Egray180/night-vision-monocular/resources/switch-16.snapshot.3/switch_SS12F15G5_4.png

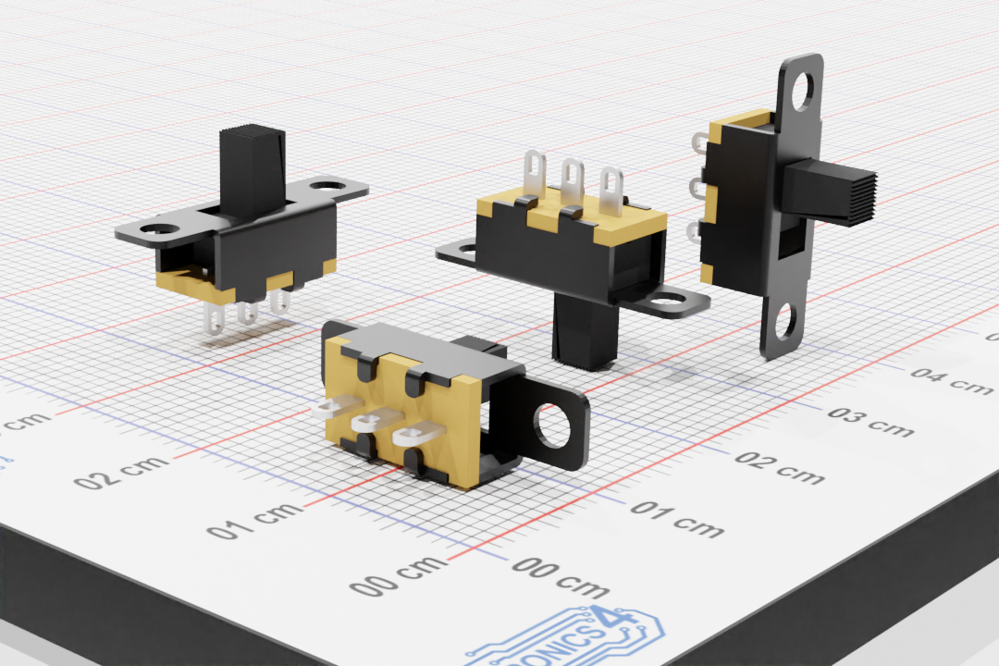
resources/switch-16.snapshot.3/switch_SS12F15G5_4.png
