Egray180/night-vision-monocular/resources/raspberry-pi-zero-2-w-1.snapshot.3/Crystal Resonator, Raspberry Pi Zero 2 W.SLDPRT

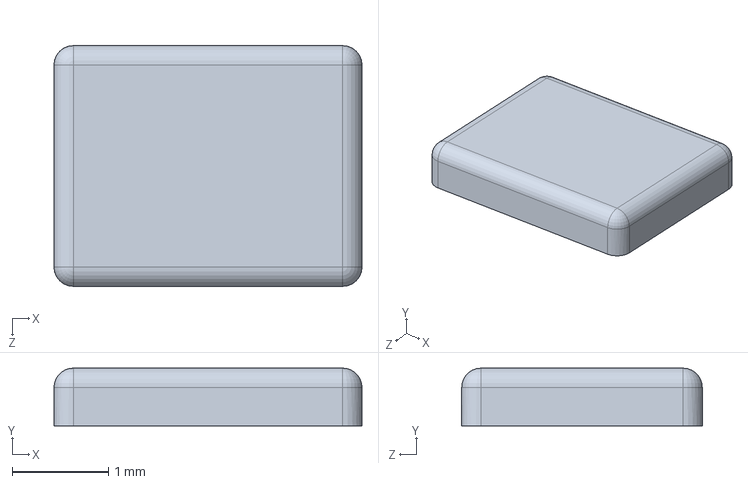
[picture p42: CAD file, 2024-07-07]
resources/raspberry-pi-zero-2-w-1.snapshot.3/Crystal Resonator, Raspberry Pi Zero 2 W.SLDPRT
3.20 x 0.6 x 2.50 mm
