Egray180/night-vision-monocular/resources/raspberry-pi-zero-2-w-1.snapshot.3/PAM2306AYPKE, Switching Voltage Regulators Dual PWM Step-Down 40uA 1A 1.5MHz, Raspberry Pi Zero 2 W.SLDPRT

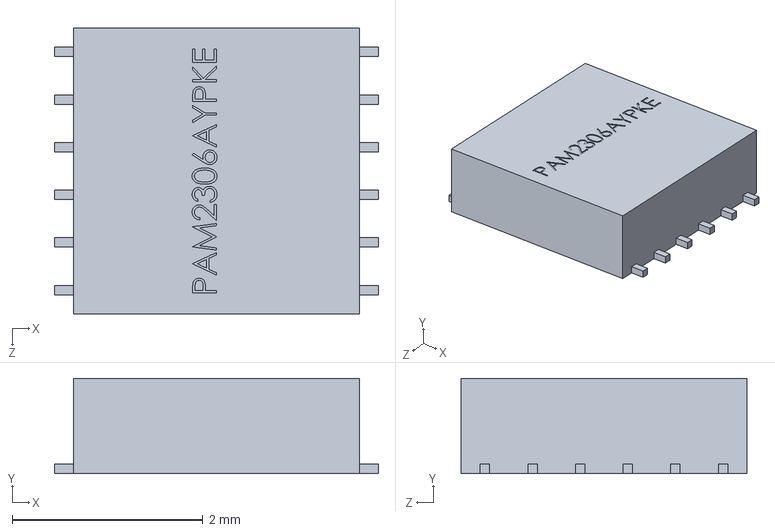
[picture p43: CAD file, 2024-07-07]
resources/raspberry-pi-zero-2-w-1.snapshot.3/PAM2306AYPKE, Switching Voltage Regulators Dual PWM Step-Down 40uA 1A 1.5MHz, Raspberry Pi Zero 2 W.SLDPRT
3.40 x 1.00 x 3.00 mm
