Egray180/night-vision-monocular/resources/raspberry-pi-zero-2-w-1.snapshot.3/SD Card Slot, Raspberry Pi Zero 2 W.SLDPRT

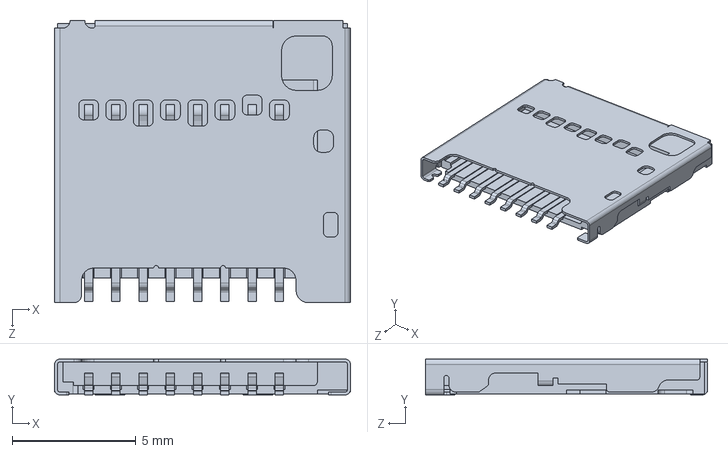
[picture p44: CAD file, 2024-07-07]
resources/raspberry-pi-zero-2-w-1.snapshot.3/SD Card Slot, Raspberry Pi Zero 2 W.SLDPRT
11.9 x 1.45 x 11.4 mm
