Egray180/night-vision-monocular/resources/raspberry-pi-zero-2-w-1.snapshot.3/Wireless Module Cover, Raspberry Pi Zero 2 W.SLDPRT

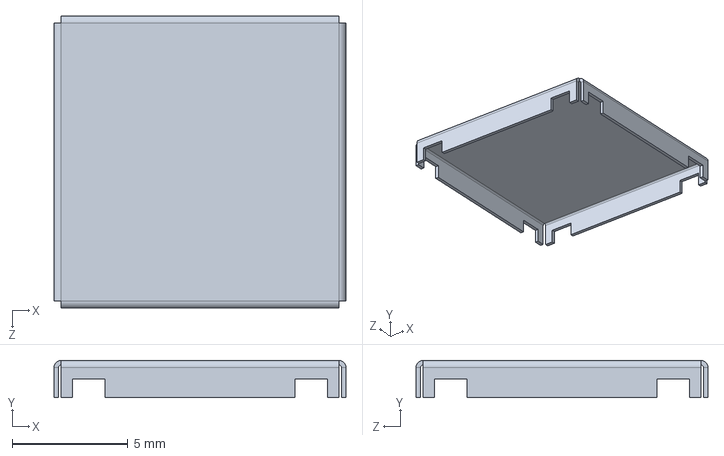
[picture p45: CAD file, 2024-07-07]
resources/raspberry-pi-zero-2-w-1.snapshot.3/Wireless Module Cover, Raspberry Pi Zero 2 W.SLDPRT
12.6 x 1.60 x 12.6 mm
