Egray180/night-vision-monocular/resources/raspberry-pi-zero-2-w-1.snapshot.3/SMD Inductor, Configurable, Raspberry Pi Zero 2 W.SLDPRT

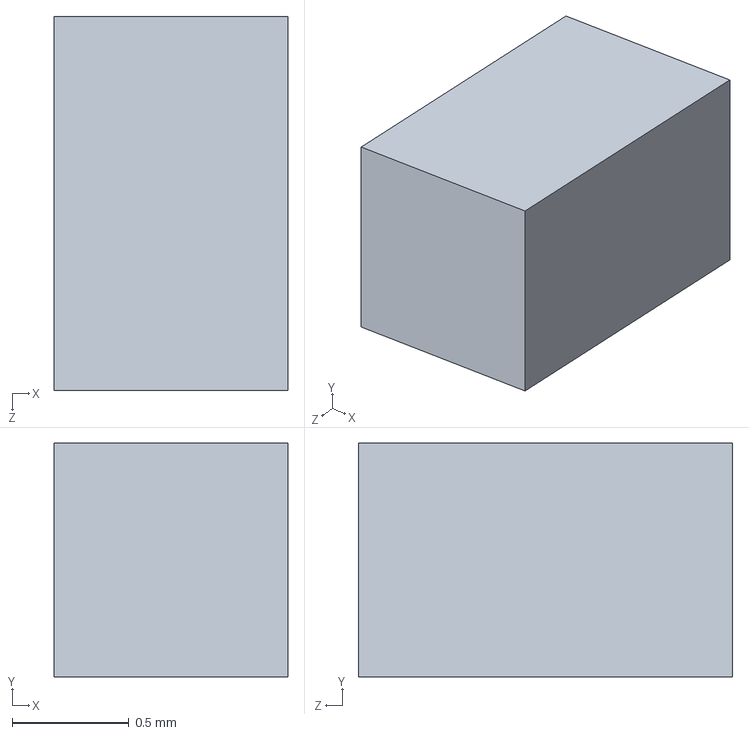
[picture p46: CAD file, 2024-07-07]
resources/raspberry-pi-zero-2-w-1.snapshot.3/SMD Inductor, Configurable, Raspberry Pi Zero 2 W.SLDPRT
1.00 x 1.00 x 1.60 mm
