Egray180/night-vision-monocular/resources/raspberry-pi-zero-2-w-1.snapshot.3/Mini HDMI Receptacle Port, Raspberry Pi Zero 2 W.SLDPRT

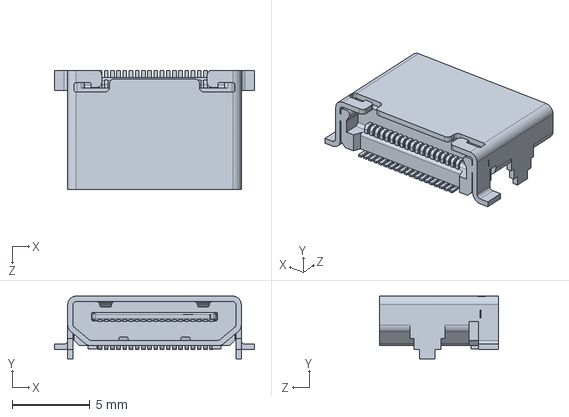
[picture p47: CAD file, 2024-07-07]
resources/raspberry-pi-zero-2-w-1.snapshot.3/Mini HDMI Receptacle Port, Raspberry Pi Zero 2 W.SLDPRT
12.9 x 4.05 x 7.70 mm
