Egray180/night-vision-monocular/resources/raspberry-pi-zero-2-w-1.snapshot.3/LED, Raspberry Pi Zero 2 W.SLDPRT

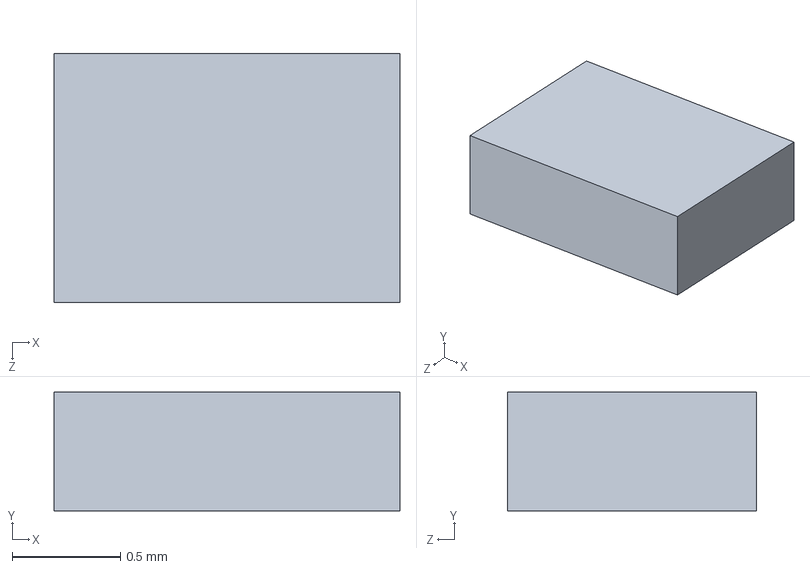
[picture p48: CAD file, 2024-07-07]
resources/raspberry-pi-zero-2-w-1.snapshot.3/LED, Raspberry Pi Zero 2 W.SLDPRT
1.60 x 0.55 x 1.15 mm
