Egray180/night-vision-monocular/resources/raspberry-pi-zero-2-w-1.snapshot.3/Diode, Schottky, Raspberry Pi Zero 2 W.SLDPRT

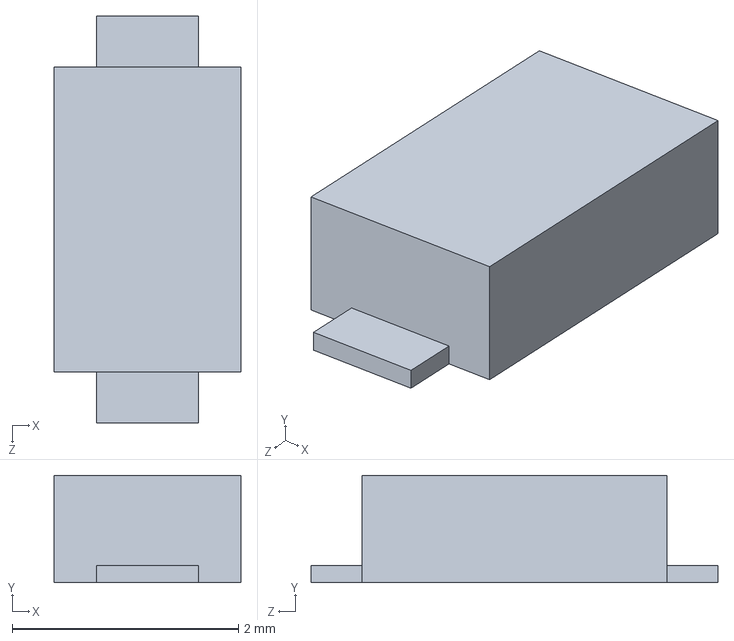
[picture p49: CAD file, 2024-07-07]
resources/raspberry-pi-zero-2-w-1.snapshot.3/Diode, Schottky, Raspberry Pi Zero 2 W.SLDPRT
1.65 x 0.95 x 3.60 mm
