Egray180/night-vision-monocular/resources/raspberry-pi-zero-2-w-1.snapshot.3/MicroUSB Port, Raspberry Pi Zero 2 W.SLDPRT

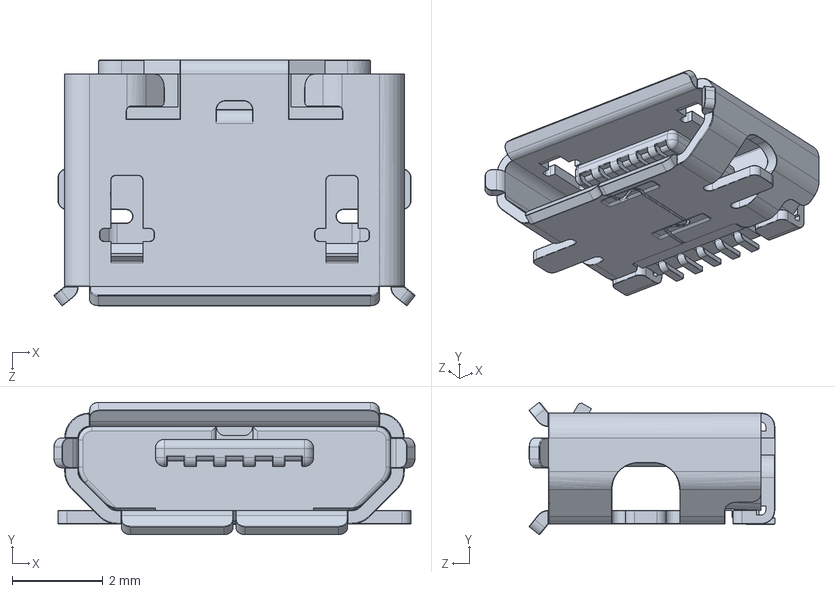
[picture p50: CAD file, 2024-07-07]
resources/raspberry-pi-zero-2-w-1.snapshot.3/MicroUSB Port, Raspberry Pi Zero 2 W.SLDPRT
7.97 x 2.92 x 5.43 mm
