Egray180/night-vision-monocular/resources/raspberry-pi-zero-2-w-1.snapshot.3/RT9081A-1BGQZA, Fixed LDO Voltage Regulator, 0.8V-5.5Vin, 140mV drop, 1.25Vout, 0.5Aout, Raspberry Pi Zero 2 W.SLDPRT

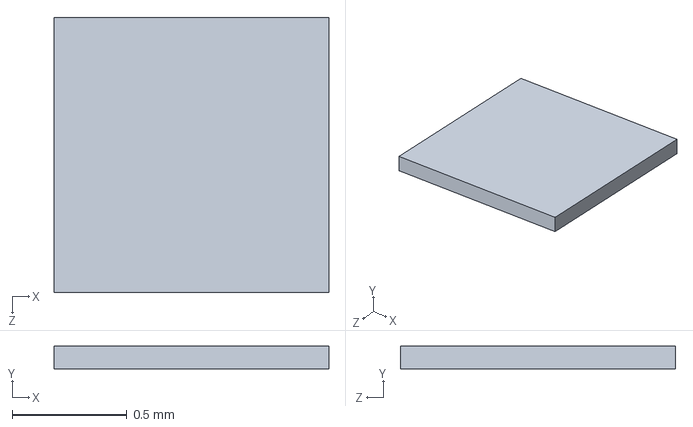
[picture p51: CAD file, 2024-07-07]
resources/raspberry-pi-zero-2-w-1.snapshot.3/RT9081A-1BGQZA, Fixed LDO Voltage Regulator, 0.8V-5.5Vin, 140mV drop, 1.25Vout, 0.5Aout, Raspberry Pi Zero 2 W.SLDPRT
1.20 x 0.1 x 1.20 mm
